gpa-fryk-industries/CDIO/fw/ice/fft/fft_twiddle_lut.vhd

library IEEE;
use IEEE.std_logic_1164.all;
use IEEE.numeric_std.all;

entity fft_twiddle_lut2 is
	
	generic (
	
		N_bit : integer := 8;
		L     : integer := 4
	);
	
	port( 
	
		
		tw_index_0 : in unsigned(L-1 downto 0);
		tw_index_1 : in unsigned(L-1 downto 0);
		
		twiddle_real_0 : out signed(N_bit downto 0);
		twiddle_imag_0 : out signed(N_bit downto 0);
		
		twiddle_real_1 : out signed(N_bit downto 0);
		twiddle_imag_1 : out signed(N_bit downto 0)
		
	);

end fft_twiddle_lut2;

architecture arch_fft_twiddle_lut2 of fft_twiddle_lut2 is
	
	signal tw0 : integer range 0 to 63;
	signal tw1 : integer range 0 to 63;			
																				 
begin

	tw0 <= to_integer(tw_index_0);
	tw1 <= to_integer(tw_index_1);

	
	process(tw0)
	begin

	case tw0 is
	
		when 0 => 
		 twiddle_real_0 <= to_signed(128, N_bit+1);
		 twiddle_imag_0 <= to_signed(0, N_bit+1);
		when 1 => 
		 twiddle_real_0 <= to_signed(127, N_bit+1);
		 twiddle_imag_0 <= to_signed(-13, N_bit+1);
		when 2 => 
		 twiddle_real_0 <= to_signed(125, N_bit+1);
		 twiddle_imag_0 <= to_signed(-25, N_bit+1);
		when 3 => 
		 twiddle_real_0 <= to_signed(122, N_bit+1);
		 twiddle_imag_0 <= to_signed(-38, N_bit+1);
		when 4 => 
		 twiddle_real_0 <= to_signed(118, N_bit+1);
		 twiddle_imag_0 <= to_signed(-49, N_bit+1);
		when 5 => 
		 twiddle_real_0 <= to_signed(112, N_bit+1);
		 twiddle_imag_0 <= to_signed(-61, N_bit+1);
		when 6 => 
		 twiddle_real_0 <= to_signed(106, N_bit+1);
		 twiddle_imag_0 <= to_signed(-72, N_bit+1);
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
		 twiddle_imag_1 <= to_signed(112, N_bit+1);
		when 54 => 
		 twiddle_real_1 <= to_signed(71, N_bit+1);
		 twiddle_imag_1 <= to_signed(106, N_bit+1);
		when 55 => 
		 twiddle_real_1 <= to_signed(81, N_bit+1);
		 twiddle_imag_1 <= to_signed(98, N_bit+1);
		when 56 => 
		 twiddle_real_1 <= to_signed(90, N_bit+1);
		 twiddle_imag_1 <= to_signed(90, N_bit+1);
		when 57 => 
		 twiddle_real_1 <= to_signed(98, N_bit+1);
		 twiddle_imag_1 <= to_signed(81, N_bit+1);
		when 58 => 
		 twiddle_real_1 <= to_signed(106, N_bit+1);
		 twiddle_imag_1 <= to_signed(71, N_bit+1);
		when 59 => 
		 twiddle_real_1 <= to_signed(112, N_bit+1);
		 twiddle_imag_1 <= to_signed(60, N_bit+1);
		when 60 => 
		 twiddle_real_1 <= to_signed(118, N_bit+1);
		 twiddle_imag_1 <= to_signed(48, N_bit+1);
		when 61 => 
		 twiddle_real_1 <= to_signed(122, N_bit+1);
		 twiddle_imag_1 <= to_signed(37, N_bit+1);
		when 62 => 
		 twiddle_real_1 <= to_signed(125, N_bit+1);
		 twiddle_imag_1 <= to_signed(24, N_bit+1);
		when 63 => 
		 twiddle_real_1 <= to_signed(127, N_bit+1);
		 twiddle_imag_1 <= to_signed(12, N_bit+1);

	end case;

	end process;
	
	
end arch_fft_twiddle_lut2;
	
	
