gpa-fryk-industries/CDIO/fw/ice/adpcm/adpcm_adapt.vhd

library IEEE;
use IEEE.std_logic_1164.all;
use IEEE.numeric_std.all;

entity adpcm_adapt is
	
	generic (
		
		N : integer := 3 -- How many stages of ADPCM do we want? N = 1 -> 2 bit, N = 2 -> 3 bit and N = 3 -> 4 bit compression.
	
	);
	
   port( 
	
		Pred_sample_load : in signed(15 downto 0);
		Pred_index_load  : in unsigned(7 downto 0);
	
		Code_in     : in unsigned(3 downto 0); -- Encoded signal. 
		Diffq_in    : in signed(15 downto 0); -- Diffq signal from inverted quantizer.
		Sample_in   : in  signed(7 downto 0); -- New sample from microphone / sound source. 
	
		Clock       : in std_logic; -- Clock signal. 8 KHz in the moment of writing this.
		Reset       : in std_logic; -- Reset signal. Reset module on '1'. 
		
		Pred_sample_out : out signed(15 downto 0);
		Pred_index_out  : out unsigned(7 downto 0);
		
		y_signal	: out signed(7 downto 0); -- Decoded output signal in decoder mode.
		
		Diff_out    : out signed(15 downto 0); -- Difference between sample and predicted sample. Send to Quantizer.
		Step_out    : out signed(15 downto 0) -- Step signal to Quantizer and inverted Quantizer.
		       
	);
end adpcm_adapt;

architecture arch_adpcm_adapt of adpcm_adapt is
	
	signal pred_sample     : signed(16 downto 0) := (others => '0'); -- Predicted sample for next cycle. Initialize as 0.
	signal pred_sample_u16 : signed(15 downto 0); -- Predicted sample for next cycle. Initialize as 0.
	signal pred_index      : integer range 0 to 88 := 0 ; -- Predicted index for next cycle. Initialize as 0.
	
	signal sample_padded : signed(15 downto 0); -- Padded sample, algorithm is working with 16 bit numbers in this implementation. 
																-- Input signal scaled to 16 bit.												
	signal step_out_i16 : integer range 0 to 32767;
	signal index_code : integer range -1 to 8;
	signal index_table_index : integer range 0 to 15;
	
begin   

	ADAPT: process(Clock, Reset, pred_index_load, pred_sample_load, Diffq_in, pred_sample) is 
	
	begin
		
		-- Go back to initial "state".
		if (Reset = '1') then
		
			pred_sample <= to_signed(to_integer(pred_sample_load),17);
			pred_sample_u16 <= pred_sample_load;
			pred_index  <= to_integer(pred_index_load);
		
		-- 
		elsif ( rising_edge(Clock) ) then
			
			-- Is the sign of Code_in negative / is MSB '1'?
			
			if(Code_in(N) = '1') then		
				pred_sample <=   to_signed( to_integer( (pred_sample_u16) - ( Diffq_in) ), 17);	
			else
				pred_sample <=   to_signed( to_integer( (pred_sample_u16) + ( Diffq_in) ), 17);	
			end if;
				
		
			if( (pred_index + index_code ) < 0 ) then
				pred_index <= 0;
			elsif( (pred_index + index_code ) > 88 ) then
				pred_index <= 88;	
			else
				pred_index <= pred_index + index_code ;
			end if;
			
		end if;

		--Prevent overflow/underflow
		
		if ( to_integer(pred_sample) >  ( (2**15) -1 ) ) then
	
			pred_sample_u16 <= to_signed( (2**15) - 1 , 16);
	
		elsif ( to_integer(pred_sample) < ( -(2**15) ) ) then
		
			pred_sample_u16 <= to_signed( -(2**15) , 16);
		
		else
			pred_sample_u16 <= to_signed( to_integer( pred_sample ), 16 );
	
		end if;
--		
	end process;
	
	
	Sample_padded <= Sample_in & "00000000"; -- Scale input signal to 16 bit.
	
	------------------------------------------------------------------------------------
	
	Pred_sample_out <= pred_sample_u16;
	Pred_index_out  <= to_unsigned(pred_index,8);
	
	------------------------------------------------------------------------------------
	
	Diff_out <=  ( Sample_padded - pred_sample_u16); 
	Step_out <= to_signed(step_out_i16 , 16 ); 
	
	y_signal <= pred_sample_u16(15 downto 8); -- Scale back output as an 8 bit number.
	
 	------------------------------------------------------------------------------------
	--Instead of making IndexTable generic, index prediction is adapted to the number N.
	--(-1, -1, -1, -1,  2, 4, 6, -1, -1, -1, -1, 2, 4, 6, 8) if N = 3
	--(-1, -1, 2, 6, -1, -1, 2, 6)                         if N = 2
	--(-1, 2,-1, 2)                                        if N = 1
			
	-- to_integer( Code_in ) * (2**(3-N) might just look a bit cryptic...

	index_table_index <= to_integer( Code_in ) * (2**(3-N));
	
	
	--LUT--
	
	process(pred_index) 
	begin
		
		case(pred_index) is
			
		when 0 => 
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
		 index_code <= -1; 
		when 10 => 
		 index_code <= -1; 
		when 11 => 
		 index_code <= -1; 
		when 12 => 
		 index_code <= 2; 
		when 13 => 
		 index_code <= 4; 
		when 14 => 
		 index_code <= 6; 
		when 15 => 
		 index_code <= 8; 
		
		end case;

	end process;
	
end arch_adpcm_adapt;
