gpa-fryk-industries/CDIO/fw/ice/fft/fft_abs_value.vhd

library IEEE;
use IEEE.std_logic_1164.all;
use IEEE.numeric_std.all;

entity fft_abs_value is

	generic (
	
		N_bit : integer := 8;
		Stage : integer := 2
	);
	
   port( 
		
		x_real : in signed(Stage + N_bit downto 0);
		x_imag : in signed(Stage + N_bit downto 0);
		
		y_abs : out unsigned(2*N_bit -1 downto 0)
				
	);
end fft_abs_value;

architecture arch_fft_abs_value of fft_abs_value is

	signal R : integer;
	signal I : integer;

begin

	R <= to_integer(abs(x_real));
	I <= to_integer(abs(x_imag));

	y_abs <= to_unsigned(R+I, 16);

	
end arch_fft_abs_value;
