gpa-fryk-industries/CDIO/fw/mcu/src/fpga/fpga_config.c

//
// Created by atmelfan on 2018-11-10.
//

#include <sched.h>
#include <stdbool.h>
#include "fpga_config.h"




char get_byte(uint32_t x){
    return 0;
}

bool fpga_configure(){



    return false;
}
