gpa-fryk-industries/CDIO/fw/mcu/src/fpga/fpga_config.h

//
// Created by atmelfan on 2018-11-10.
//

#ifndef PROJECT_FPGA_CONFIG_H
#define PROJECT_FPGA_CONFIG_H

#include <stdbool.h>
#include <stdint.h>

bool fpga_configure();

char get_byte(uint32_t x);

#endif //PROJECT_FPGA_CONFIG_H
